Miceuz/SolarCampingLentern/Firmware/millis.c

/*
  wiring.c - Partial implementation of the Wiring API for the ATmega8.
  Part of Arduino - http://www.arduino.cc/

  Copyright (c) 2005-2006 David A. Mellis

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
  You should have received a copy of the GNU Lesser General
  Public License along with this library; if not, write to the
  Free Software Foundation, Inc., 59 Temple Place, Suite 330,
  Boston, MA  02111-1307  USA
*/

#include <avr/interrupt.h>
#include <avr/io.h>
#include <avr/sfr_defs.h>
#include <avr/wdt.h>

#define clockCyclesPerMicrosecond() (F_CPU / 1000000L)
#define clockCyclesToMicroseconds(a) ((a) / clockCyclesPerMicrosecond())

#define MICROSECONDS_PER_TIMER0_OVERFLOW (clockCyclesToMicroseconds(64 * 256))
#define MILLIS_INC (MICROSECONDS_PER_TIMER0_OVERFLOW / 1000)

#define FRACT_INC ((MICROSECONDS_PER_TIMER0_OVERFLOW % 1000) >> 3)
#define FRACT_MAX (1000 >> 3)

volatile unsigned long timer0_overflow_count = 0;
volatile unsigned long timer0_millis = 0;
static unsigned char timer0_fract = 0;

ISR(TIMER0_OVF_vect) {
  // copy these to local variables so they can be stored in registers
  // (volatile variables must be read from memory on every access)
  unsigned long m = timer0_millis;
  unsigned char f = timer0_fract;

  m += MILLIS_INC;
  f += FRACT_INC;
  if (f >= FRACT_MAX) {
    f -= FRACT_MAX;
    m += 1;
  }

  timer0_fract = f;
  timer0_millis = m;
  timer0_overflow_count++;
}

unsigned long millis() {
  unsigned long m;
  uint8_t oldSREG = SREG;

  // disable interrupts while we read timer0_millis or we might get an
  // inconsistent value (e.g. in the middle of a write to timer0_millis)
  cli();
  m = timer0_millis;
  SREG = oldSREG;

  return m;
}

unsigned long micros() {
  unsigned long m;
  uint8_t oldSREG = SREG, t;

  cli();
  m = timer0_overflow_count;
  t = TCNT0;

  if ((TIFR0 & _BV(TOV0)) && (t < 255))
    m++;
  SREG = oldSREG;

  return ((m << 8) + t) * (64 / clockCyclesPerMicrosecond());
}

void millisInit() {
  TCCR0B |= _BV(CS01);
  TCCR0B |= _BV(CS00);
  // enable timer 0 overflow interrupt
  TIMSK0 |= _BV(TOIE0);
}

void delay(uint16_t ms) {
  uint32_t stop = millis() + ms;
  while (millis() < stop) {
    // wait
    wdt_reset();
  }
}
